RL95/SmartWeatherVane/CAD/SolidWorks/SolenoidSupport.SLDPRT

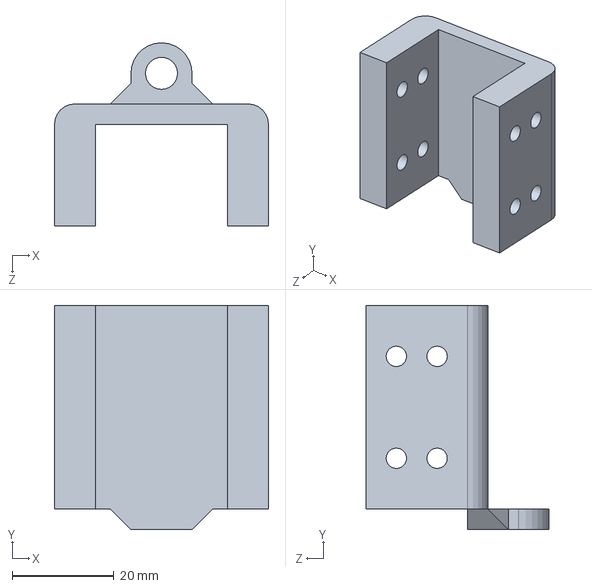
[picture p19: CAD file, 2023-05-16]
CAD/SolidWorks/SolenoidSupport.SLDPRT
42.0 x 44.0 x 36.0 mm
