RL95/SmartWeatherVane/CAD/SolidWorks/AvidCaliper.SLDPRT

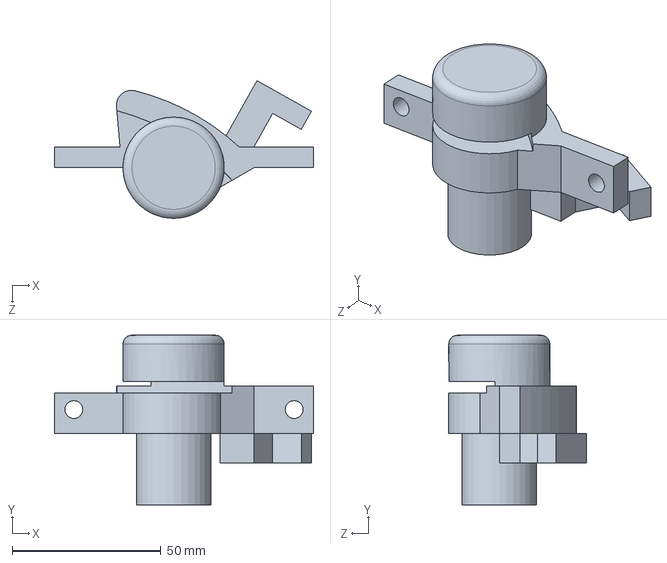
[picture p20: CAD file, 2023-05-15]
CAD/SolidWorks/AvidCaliper.SLDPRT
87.0 x 57.0 x 46.2 mm
