RL95/SmartWeatherVane/CAD/SolidWorks/PulleyHTD5M12T.SLDPRT

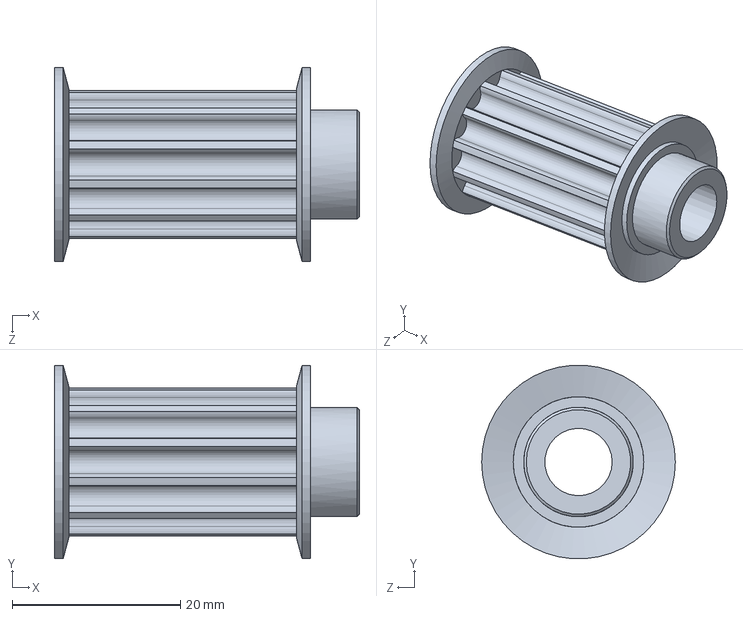
[picture p21: CAD file, 2023-05-15]
CAD/SolidWorks/PulleyHTD5M12T.SLDPRT
36.2 x 22.9 x 23.0 mm
