RL95/SmartWeatherVane/CAD/SolidWorks/PulleyHTD3M44T.SLDPRT

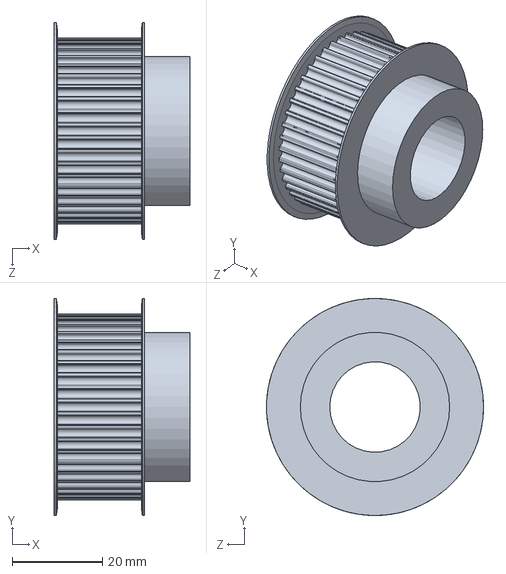
[picture p22: CAD file, 2023-05-15]
CAD/SolidWorks/PulleyHTD3M44T.SLDPRT
30.0 x 48.0 x 48.0 mm
