RL95/SmartWeatherVane/CAD/SolidWorks/ShaftConnect.SLDPRT

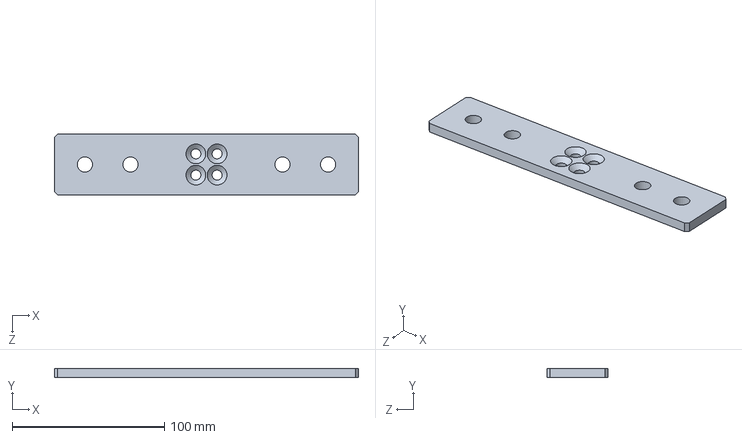
[picture p23: CAD file, 2023-05-15]
CAD/SolidWorks/ShaftConnect.SLDPRT
200.0 x 6.00 x 40.0 mm
