RL95/SmartWeatherVane/CAD/SolidWorks/Stepper103H7823-5740.SLDPRT

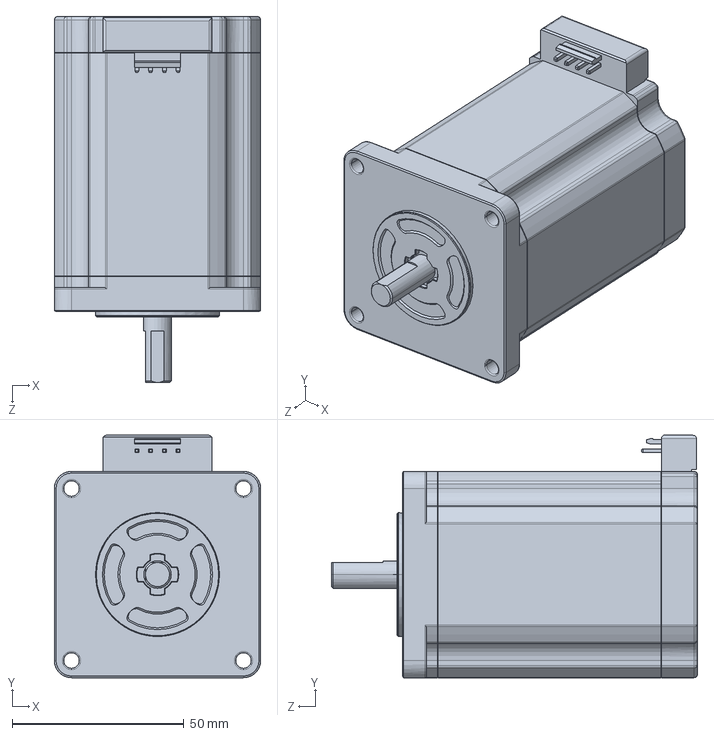
[picture p24: CAD file, 2023-05-15]
CAD/SolidWorks/Stepper103H7823-5740.SLDPRT
60.0 x 70.5 x 106.4 mm
