RL95/SmartWeatherVane/CAD/SolidWorks/PulleyHTD3M14T.SLDPRT

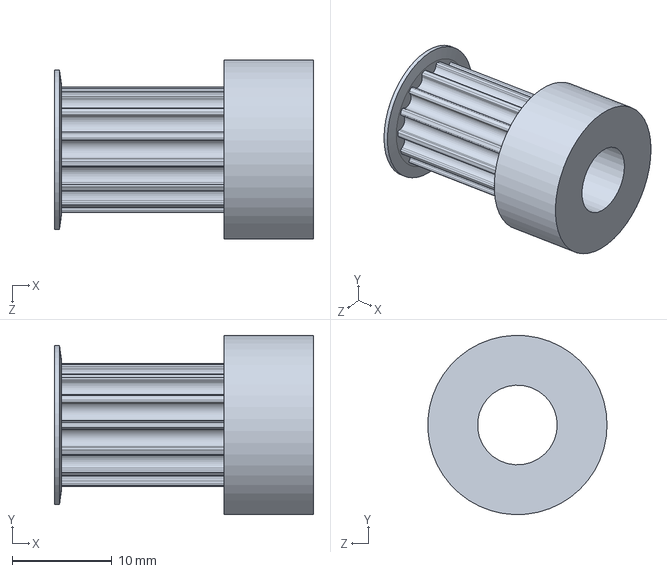
[picture p25: CAD file, 2023-05-15]
CAD/SolidWorks/PulleyHTD3M14T.SLDPRT
26.0 x 18.0 x 18.0 mm
