RL95/SmartWeatherVane/CAD/SolidWorks/PulleyHTD5M40T.SLDPRT

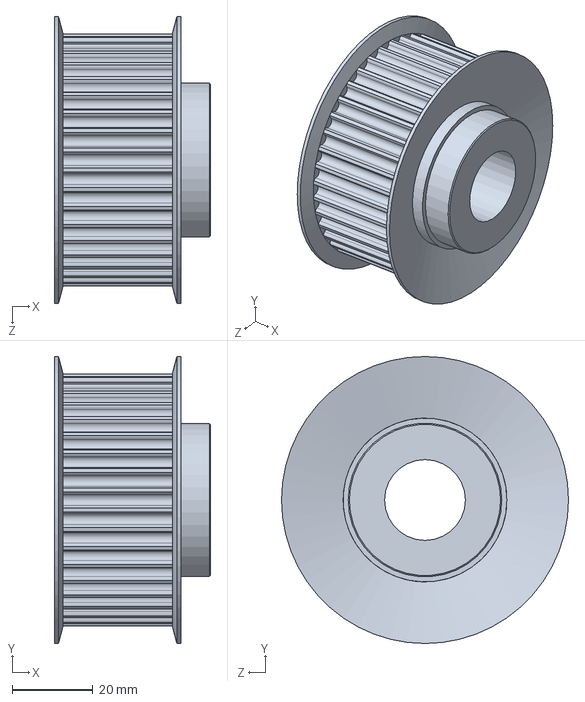
[picture p26: CAD file, 2023-05-15]
CAD/SolidWorks/PulleyHTD5M40T.SLDPRT
38.7 x 71.0 x 71.0 mm
