RL95/SmartWeatherVane/CAD/SolidWorks/NEMA23-Motor-Mounting-Plate.SLDPRT

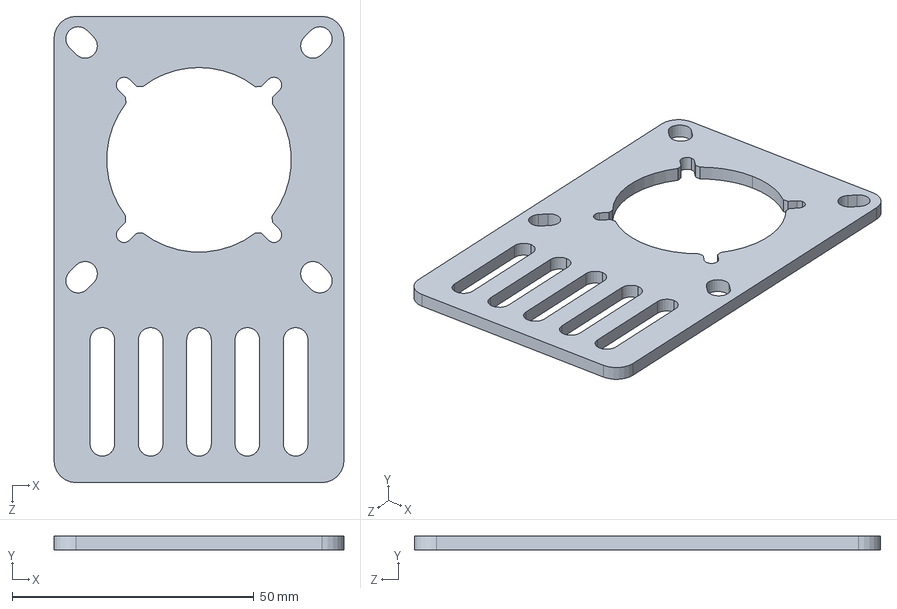
[picture p27: CAD file, 2023-05-15]
CAD/SolidWorks/NEMA23-Motor-Mounting-Plate.SLDPRT
60.0 x 3.00 x 96.5 mm
