RL95/SmartWeatherVane/CAD/SolidWorks/40x40x125.SLDPRT

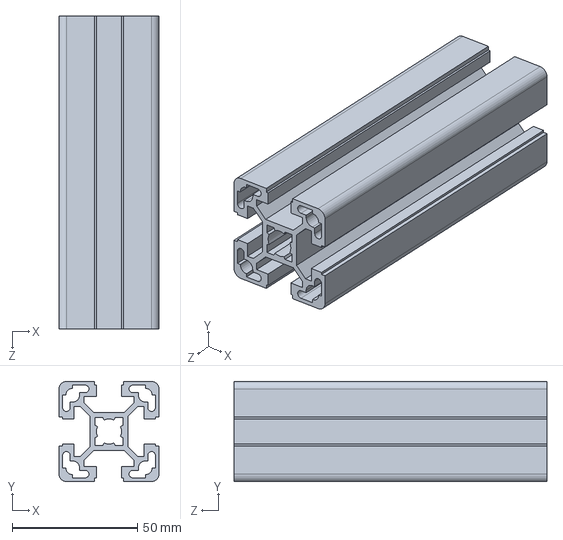
[picture p28: CAD file, 2023-05-15]
CAD/SolidWorks/40x40x125.SLDPRT
40.0 x 40.0 x 125.0 mm
