RL95/SmartWeatherVane/CAD/SolidWorks/40x40x247.SLDPRT

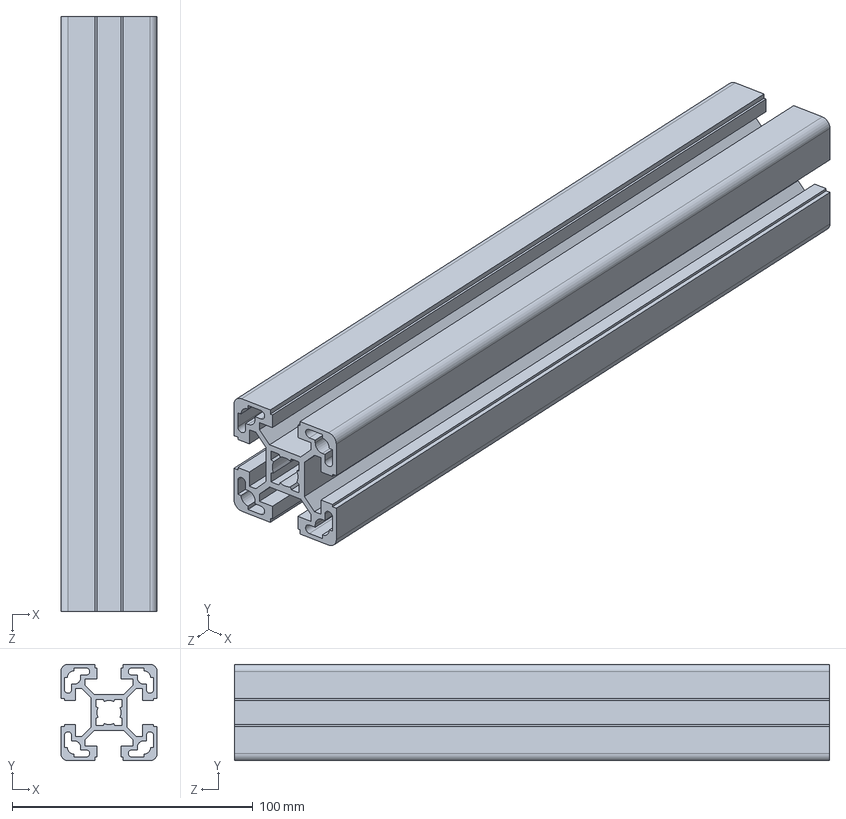
[picture p29: CAD file, 2023-05-15]
CAD/SolidWorks/40x40x247.SLDPRT
40.0 x 40.0 x 247.0 mm
