RL95/SmartWeatherVane/CAD/SolidWorks/DRV8825.SLDPRT

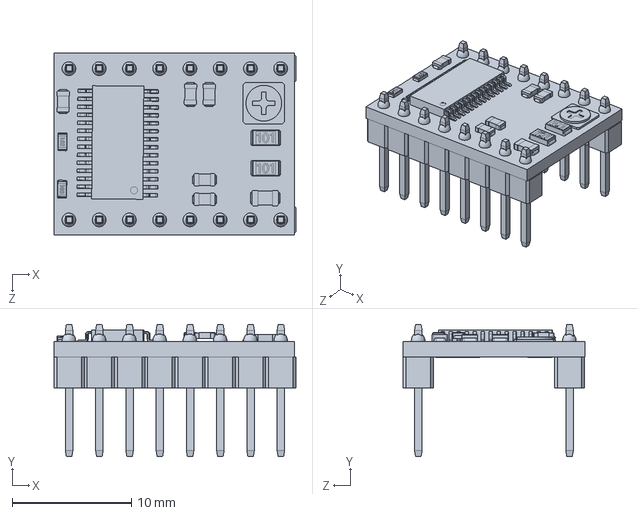
[picture p30: CAD file, 2023-05-15]
CAD/SolidWorks/DRV8825.SLDPRT
20.3 x 11.1 x 15.2 mm
