RL95/SmartWeatherVane/CAD/SolidWorks/heatsink_14-5x15x13.SLDPRT

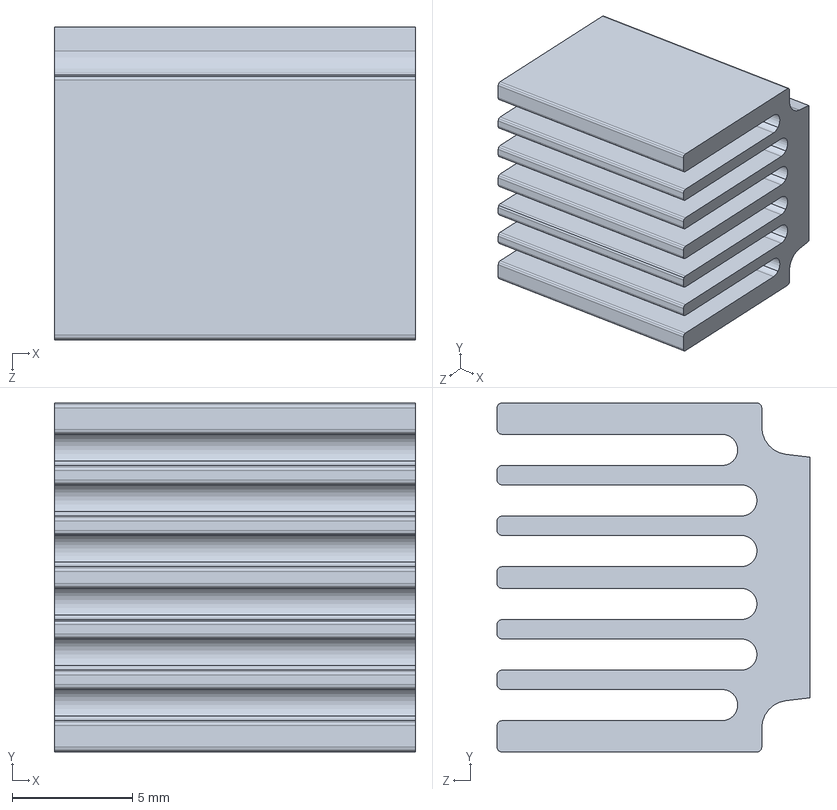
[picture p31: CAD file, 2023-05-15]
CAD/SolidWorks/heatsink_14-5x15x13.SLDPRT
15.0 x 14.5 x 13.0 mm
