RL95/SmartWeatherVane/CAD/SolidWorks/40x40x167.SLDPRT

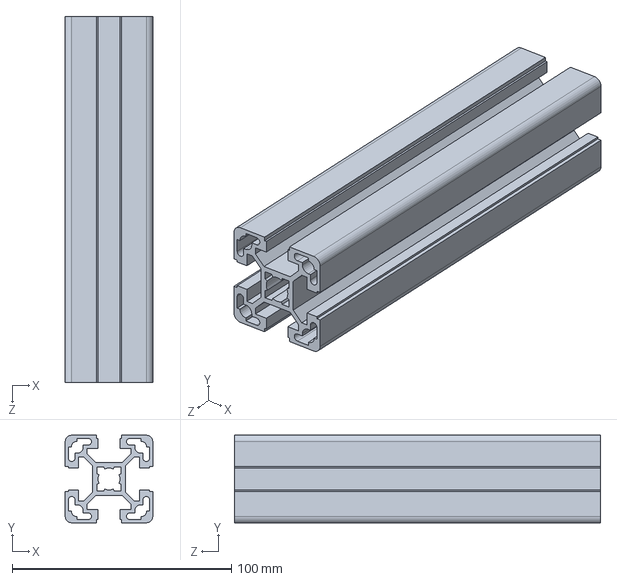
[picture p32: CAD file, 2023-05-15]
CAD/SolidWorks/40x40x167.SLDPRT
40.0 x 40.0 x 167.0 mm
