RL95/SmartWeatherVane/CAD/SolidWorks/heatsink_9x9x12.SLDPRT

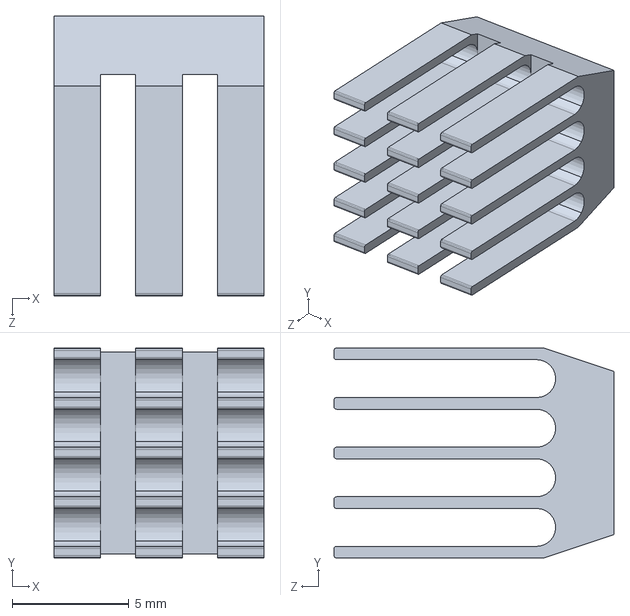
[picture p33: CAD file, 2023-05-15]
CAD/SolidWorks/heatsink_9x9x12.SLDPRT
9.00 x 9.00 x 12.0 mm
