RL95/SmartWeatherVane/CAD/SolidWorks/40x40x200.SLDPRT

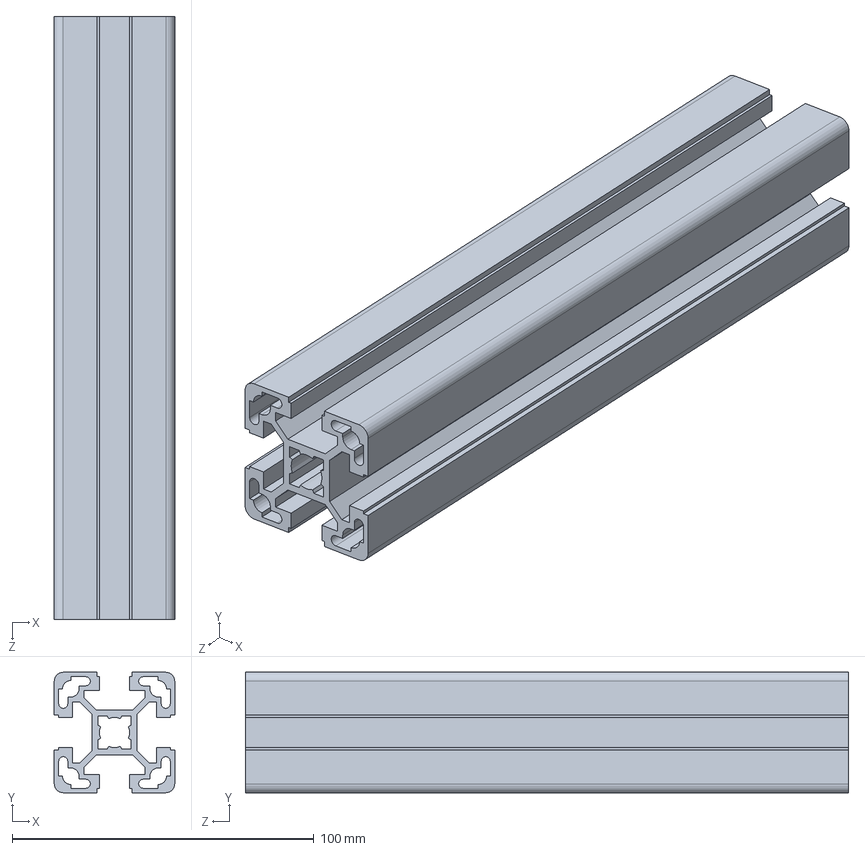
[picture p34: CAD file, 2023-05-15]
CAD/SolidWorks/40x40x200.SLDPRT
40.0 x 40.0 x 200.0 mm
