RL95/SmartWeatherVane/CAD/SolidWorks/AS5048A-EK-AB.SLDPRT

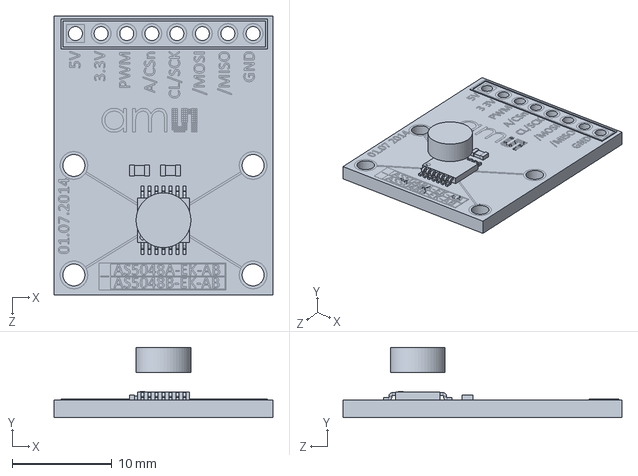
[picture p35: CAD file, 2023-05-15]
CAD/SolidWorks/AS5048A-EK-AB.SLDPRT
22.0 x 7.05 x 28.0 mm
