RL95/SmartWeatherVane/CAD/SolidWorks/40x40x3000.SLDPRT

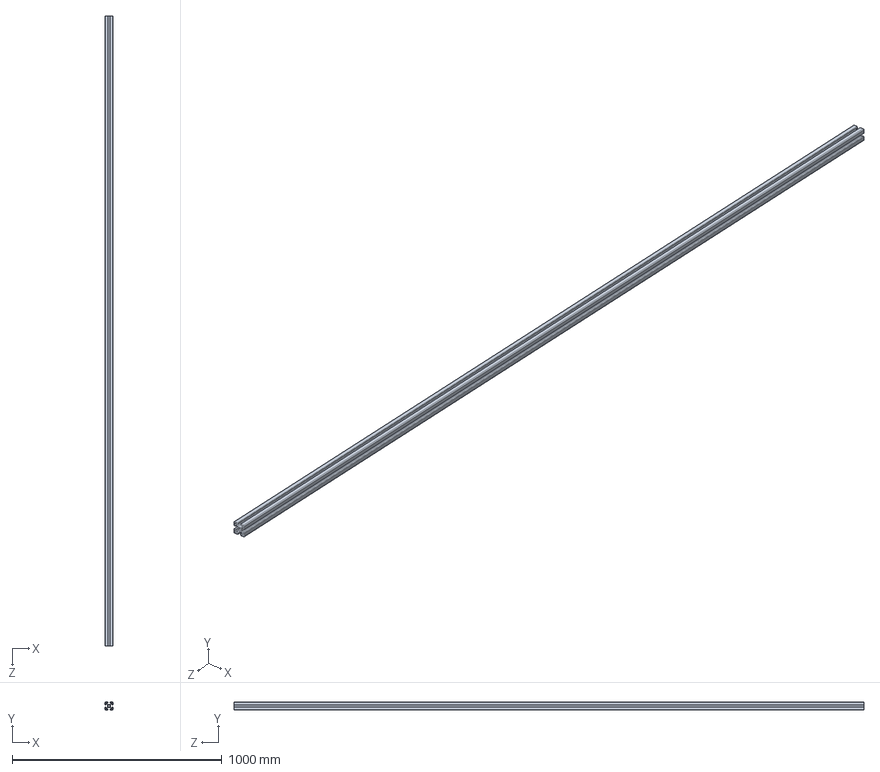
[picture p36: CAD file, 2023-05-15]
CAD/SolidWorks/40x40x3000.SLDPRT
40.0 x 40.0 x 3000.0 mm
