RL95/SmartWeatherVane/CAD/SolidWorks/AvidCaliperSupport.SLDPRT

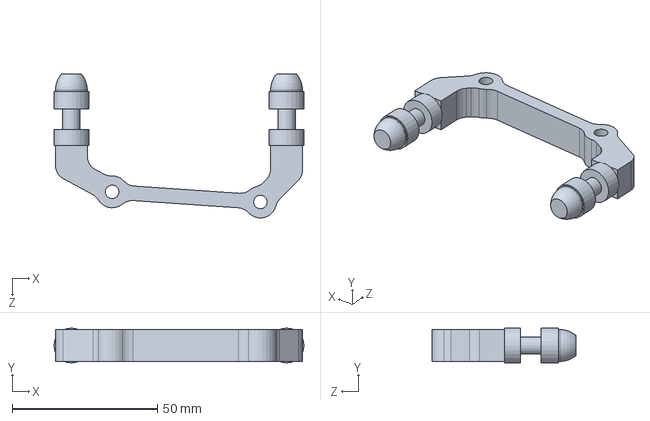
[picture p37: CAD file, 2023-05-15]
CAD/SolidWorks/AvidCaliperSupport.SLDPRT
86.0 x 12.0 x 49.5 mm
