RL95/SmartWeatherVane/CAD/SolidWorks/AvidDisc160mm.SLDPRT

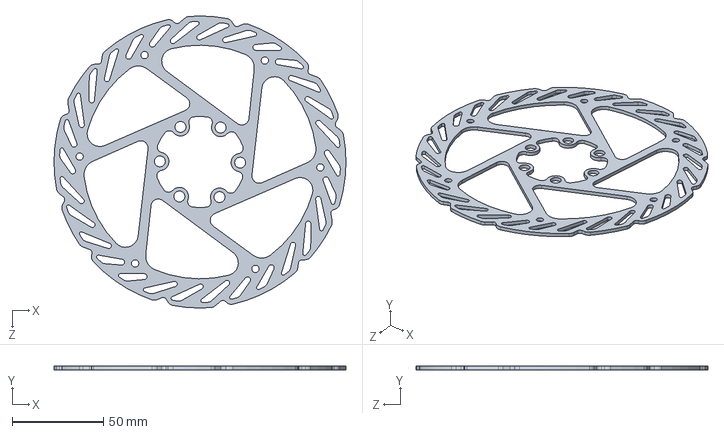
[picture p38: CAD file, 2023-05-15]
CAD/SolidWorks/AvidDisc160mm.SLDPRT
160.0 x 2.00 x 160.0 mm
