RL95/SmartWeatherVane/CAD/SolidWorks/MotorMountingPlate.SLDPRT

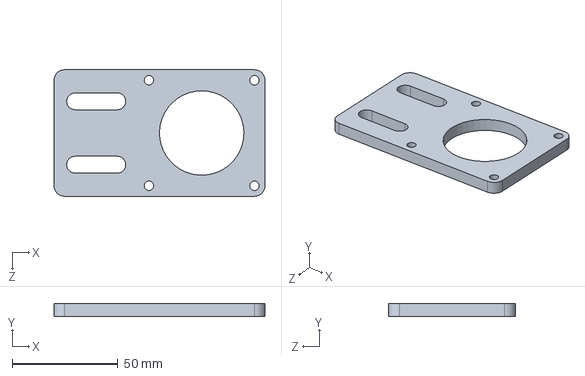
[picture p39: CAD file, 2023-05-15]
CAD/SolidWorks/MotorMountingPlate.SLDPRT
100.0 x 6.00 x 60.0 mm
