RL95/SmartWeatherVane/Firmware/Core/Src/Drivers/DRV_motion_profiling.h

/*
 * DRV_motion_profiling.h
 *
 *  Created on: June 12, 2023
 *      Author: R.Lin
 */

#ifndef SRC_DRIVERS_DRV_MOTION_PROFILING_H_
#define SRC_DRIVERS_DRV_MOTION_PROFILING_H_

#include "main.h"

#endif /* SRC_DRIVERS_DRV_MOTION_PROFILING_H_ */
