RL95/SmartWeatherVane/Firmware/Core/Src/SmartWeatherVane_main.h

/*
 * SmartWeatherVane_main.h
 *
 *  Created on: 22 May 2023
 *      Author: R.Lin
 */

#ifndef SRC_SMARTWEATHERVANE_MAIN_H_
#define SRC_SMARTWEATHERVANE_MAIN_H_

#include <main.h>
#include <stdlib.h>
#include <stdio.h>
#include <math.h>
#include "stdbool.h"
#include "stdarg.h"
#include "string.h"
#include "FSM.h"
#include "Drivers/DRV_timer_callback.h"
#include "Drivers/DRV_AS5048A.h"
#include "Drivers/DRV_TMC2660.h"
#include "Drivers/DRV_PWM.h"
#include "Drivers/DRV_motion_profiling.h"
#include "Drivers/DRV_uart_TxRx.h"

void SmartWeatherVane_main();
void Timer_Callback_10Hz();
void Timer_Callback_1kHz();
int _write(int file, char *ptr, int len);

extern UART_HandleTypeDef huart2;

#endif /* SRC_SMARTWEATHERVANE_MAIN_H_ */
