RL95/SmartWeatherVane/Firmware/Core/Src/FSM.c

/*
 * FSM.c
 *
 *  Created on: Jun 20, 2023
 *      Author: R.Lin
 */

#include "FSM.h"

AS5048A Encoder;

float angle_offset = 0;
float angle = 0;
uint16_t raw_angle = 0;
float target_angle = 0;

bool stream_en = 0;
bool stream_once = 0;
bool brake_state = 1;
bool move_to_flag = 0;
bool jog_flag = 0;
float input_val = 0;

void init_FSM(){
	// initialise magnetic absolute encoder
	AS5048A_init(&Encoder, &hspi2, AS5048_CS_GPIO_Port, AS5048_CS_Pin);
	HAL_Delay(100);
}

void step_FSM_menu(){
	switch(UART_Rx_data[0])
	    {
	        case 'm': // move to X angle
	        	UART_Rx_data[0] = '*';
	        	get_val_flag = 1;
	        	move_to_flag = 1;

	            break;

	        case 'j': // move to X angle
	        	UART_Rx_data[0] = '*';
	        	get_val_flag = 1;
	        	jog_flag = 1;

	            break;

	        case 's': // Stream angle on UART
	        	UART_Rx_data[0] = '*';
	        	stream_en = 1;
	            break;

	        case 'a': // Stream angle on UART once
	        	UART_Rx_data[0] = '*';
	        	stream_once = 1;
	            break;

	        case 'b': // Set brake state
	        	UART_Rx_data[0] = '*';
	        	brake_state = !brake_state;
	        	char set_brake_msg[31];
				snprintf(set_brake_msg, sizeof set_brake_msg, "Brake toggled. New state : %d\r\n", brake_state);
				// send through uart
				HAL_UART_Transmit(&huart2, (uint8_t *)&set_brake_msg, sizeof(set_brake_msg), 100);
	            break;

	        case 'l': // get brake state
	        	UART_Rx_data[0] = '*';
	        	char set_brake_state_msg[18];
				snprintf(set_brake_state_msg, sizeof set_brake_state_msg, "Brake state : %d\r\n", brake_state);
				// send through uart
				HAL_UART_Transmit(&huart2, (uint8_t *)&set_brake_state_msg, sizeof(set_brake_state_msg), 100);
	            break;

	        case 'z': // Set current angle to zero
	        	UART_Rx_data[0] = '*';
	        	angle_offset = AS5048A_read2angle(&Encoder, raw_angle);
	        	char set_zero_msg[16];
				snprintf(set_zero_msg, sizeof set_zero_msg, "New Zero set!\r\n");
				// send through uart
				HAL_UART_Transmit(&huart2, (uint8_t *)&set_zero_msg, sizeof(set_zero_msg), 100);
	            break;

	        case '\e': // Escape all task and go back to menu
	        	UART_Rx_data[0] = '*';
	        	stream_en = 0;
	        	UART_send_instruction_msg();
	            break;

	        case '*': // Do nothing
	            break;

	        default: // Invalid message received
	        	if(!get_val_flag && !get_val_done_flag){
		        	UART_Rx_data[0] = '*';
		        	char invalid_zero_msg[19];
					snprintf(invalid_zero_msg, sizeof invalid_zero_msg, "INVALID COMMAND!\r\n");
					// send through uart
					HAL_UART_Transmit(&huart2, (uint8_t *)&invalid_zero_msg, sizeof(invalid_zero_msg), 100);
	        	}
	    }
}


void step_FSM_retval(){
	if(get_val_done_flag){
		UART_Rx_data[0] = '*';
		// extract value
		cmd_buffer[cmd_buffer_end_idx] = ' ';
		input_val = atof(cmd_buffer);
		//TODO improve input validity check
		// validity check
		if(input_val == 0 && cmd_buffer[0] != '0'){
        	char invalid_zero_msg[19];
			snprintf(invalid_zero_msg, sizeof invalid_zero_msg, "INVALID COMMAND!\r\n");
			// send through uart
			HAL_UART_Transmit(&huart2, (uint8_t *)&invalid_zero_msg, sizeof(invalid_zero_msg), 100);
		}
		else{
			if(move_to_flag){
	        	char move_to_msg[25];
				snprintf(move_to_msg, sizeof move_to_msg, "moving to %.3f\r\n*", input_val);
				// truncate buffer at newline character
				char line_end = '*';
				char *ptr = strchr(move_to_msg, line_end);
				if(ptr){
					uint16_t size = ptr - move_to_msg;
					// send through uart
					HAL_UART_Transmit(&huart2, (uint8_t *)&move_to_msg, size, 100);
				}
				target_angle = input_val;
				move_to_flag = 0;
			}
			else if(jog_flag){
	        	char jog_msg[25];
				snprintf(jog_msg, sizeof jog_msg, "jog %.3f\r\n*", input_val);
				// truncate buffer at newline character
				char line_end = '*';
				char *ptr = strchr(jog_msg, line_end);
				if(ptr){
					uint16_t size = ptr - jog_msg;
					// send through uart
					HAL_UART_Transmit(&huart2, (uint8_t *)&jog_msg, size, 100);
				}
				target_angle = target_angle + input_val;
				jog_flag = 0;
			}
		}
		cmd_buffer_end_idx = 0;
		get_val_done_flag = 0;
		memset(&cmd_buffer, ' ', sizeof(cmd_buffer)); // clear array
	}
}

float get_FSM_target_angle(){
	return target_angle;
}

void update_current_angle(){
	// get angle
	raw_angle = AS5048A_getRawRotation(&Encoder);
	float angle_temp =  AS5048A_read2angle(&Encoder, raw_angle) - angle_offset;
	angle = AS5048A_normalize(&Encoder,angle_temp);
}

float get_current_angle(){
	return angle;
}

void step_FSM_sendval(){
	if(stream_en || stream_once){
		char uart_tx_buffer[1024];
		snprintf(uart_tx_buffer, sizeof uart_tx_buffer, "%.3f \r\n", get_current_angle());
		// truncate buffer at newline character
		char line_end = '\n';
		char *ptr = strchr(uart_tx_buffer, line_end);
		if(ptr){
			uint16_t size = ptr - uart_tx_buffer + 1;
			// send through uart
			HAL_UART_Transmit(&huart2, (uint8_t *)&uart_tx_buffer, size, 100);
		}
		// reset stream once flag
		if (stream_once) stream_once = 0;
	}
}
