RL95/SmartWeatherVane/Firmware/Core/Src/Drivers/LUT_jerk_limited_profile.h

/*
 * LUT_jerk_limited_profile.h
 *
 *  Created on: June 12, 2023
 *      Author: R.Lin
 */

#ifndef SRC_DRIVERS_LUT_JERK_LIMITED_PROFILE_H_
#define SRC_DRIVERS_LUT_JERK_LIMITED_PROFILE_H_



#endif /* SRC_DRIVERS_LUT_JERK_LIMITED_PROFILE_H_ */
